nguyenkduy28/vlc-system-project/ref/Block diagram/Bit Sampling Process for-2026-04-19-093058.png

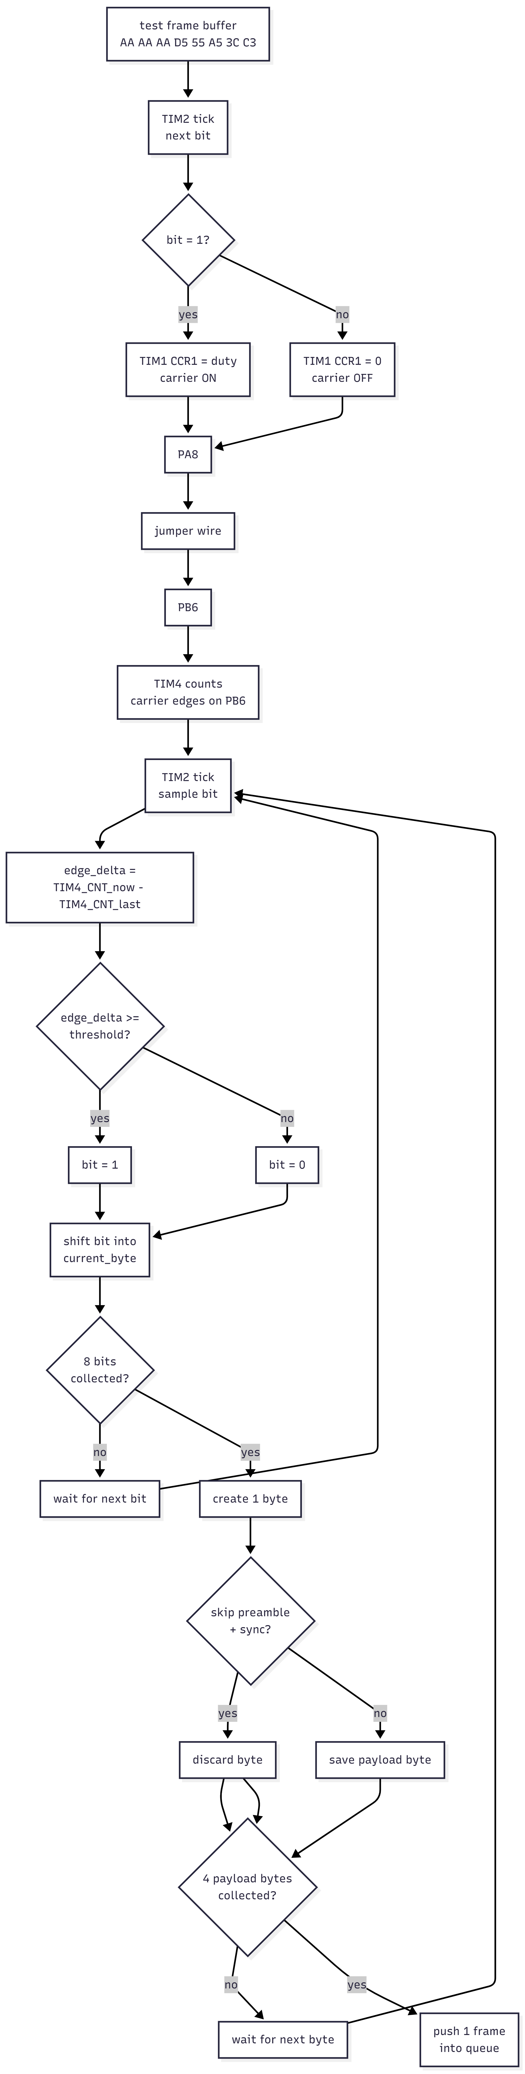
ref/Block diagram/Bit Sampling Process for-2026-04-19-093058.png
