nguyenkduy28/vlc-system-project/ref/Block diagram/TX_IDLE to CARRIER ON Flow-2026-04-19-093544.png

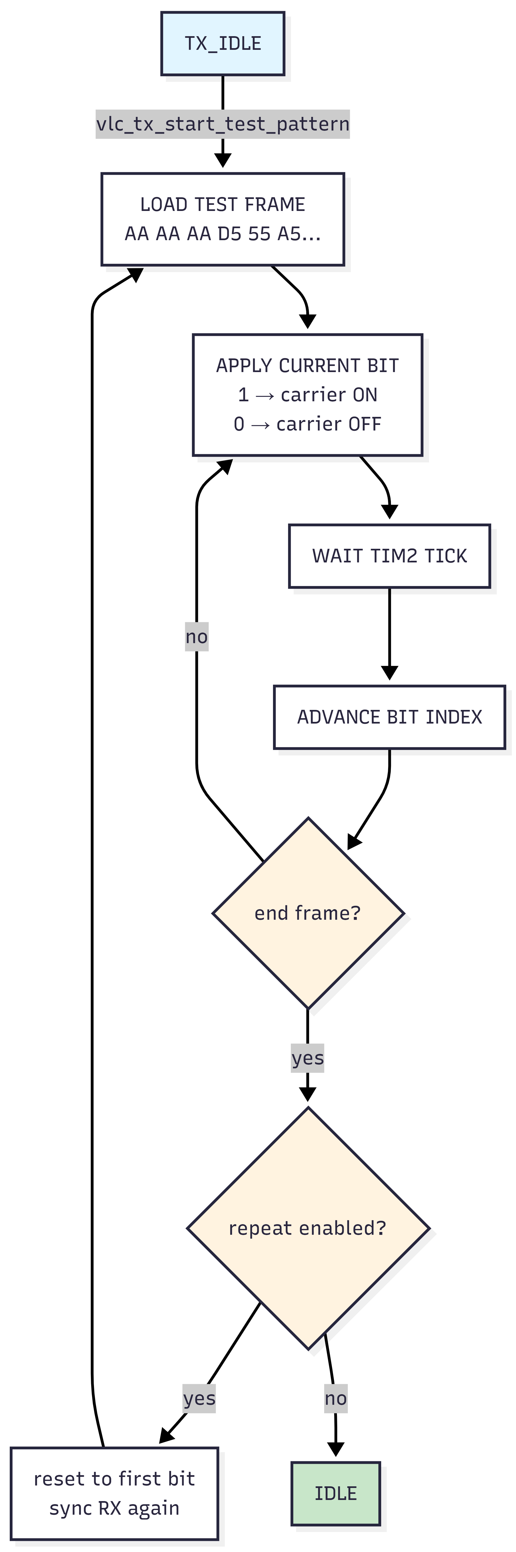
ref/Block diagram/TX_IDLE to CARRIER ON Flow-2026-04-19-093544.png
