nguyenkduy28/vlc-system-project/ref/FILTER/HPF_1KHZ.jpg

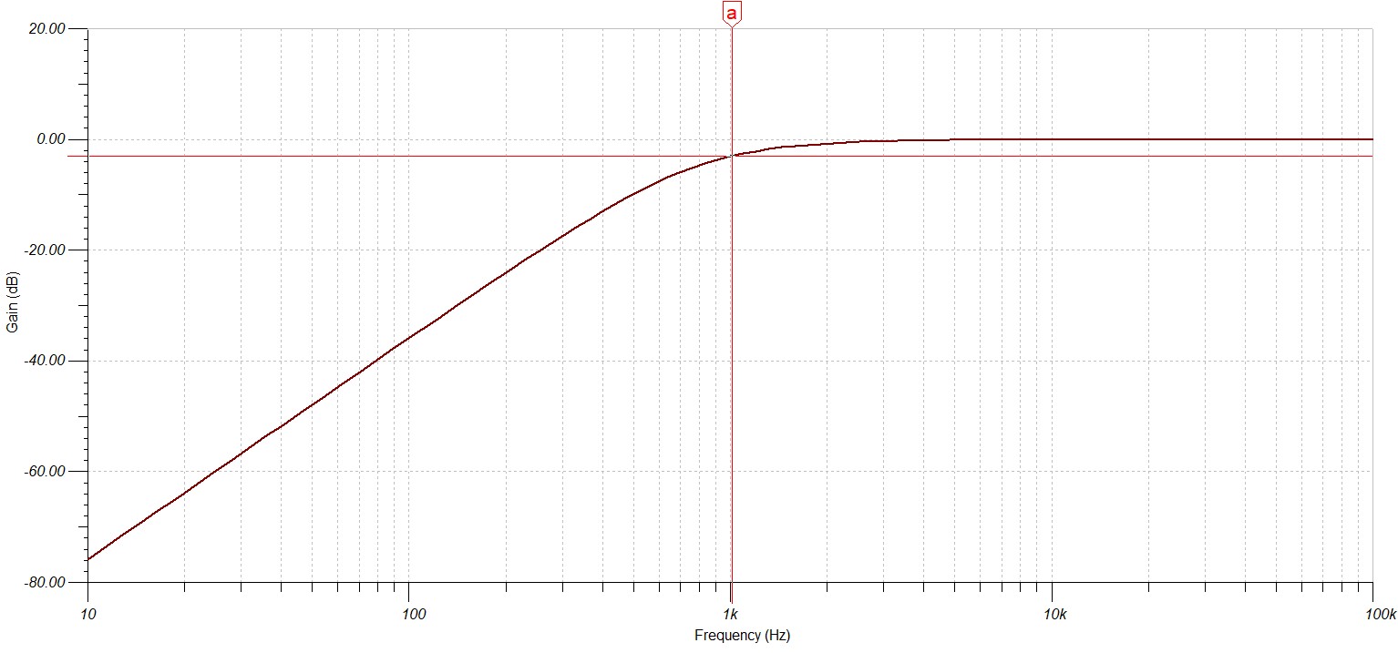
ref/FILTER/HPF_1KHZ.jpg
