nguyenkduy28/vlc-system-project/ref/ING/BU_8MHz.png

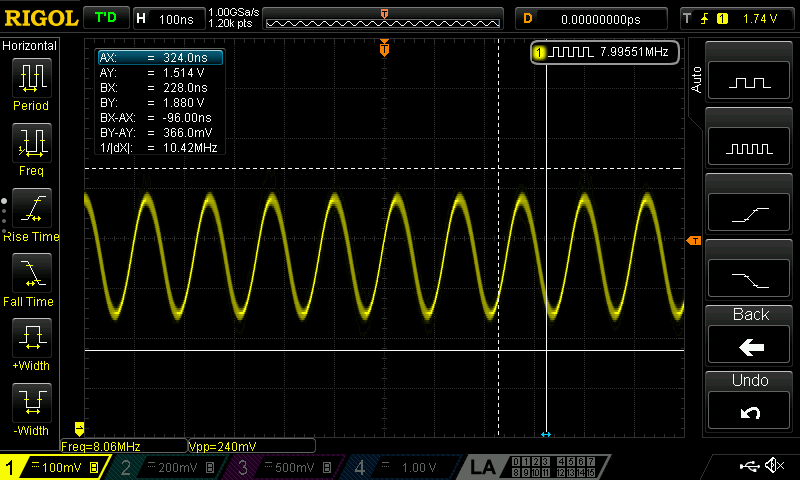
ref/ING/BU_8MHz.png
