nguyenkduy28/vlc-system-project/ref/ING/Carrier_1Mhz.png

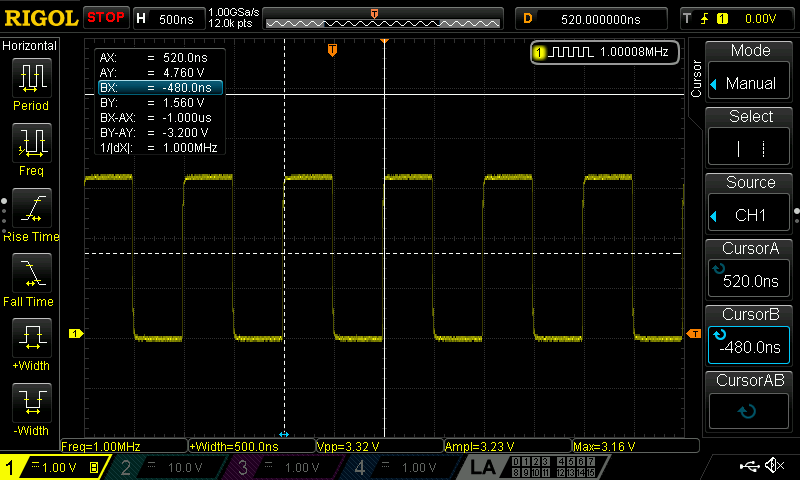
ref/ING/Carrier_1Mhz.png
