nguyenkduy28/vlc-system-project/ref/ING/flow.png

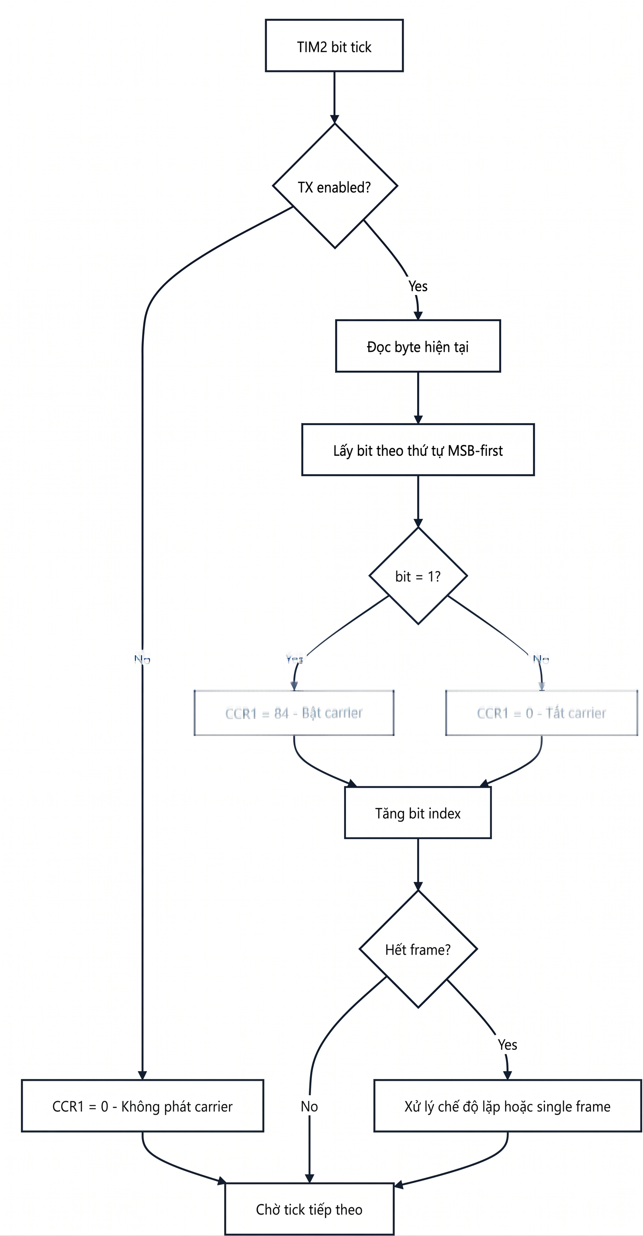
ref/ING/flow.png
