nguyenkduy28/vlc-system-project/ref/ING/layer.png

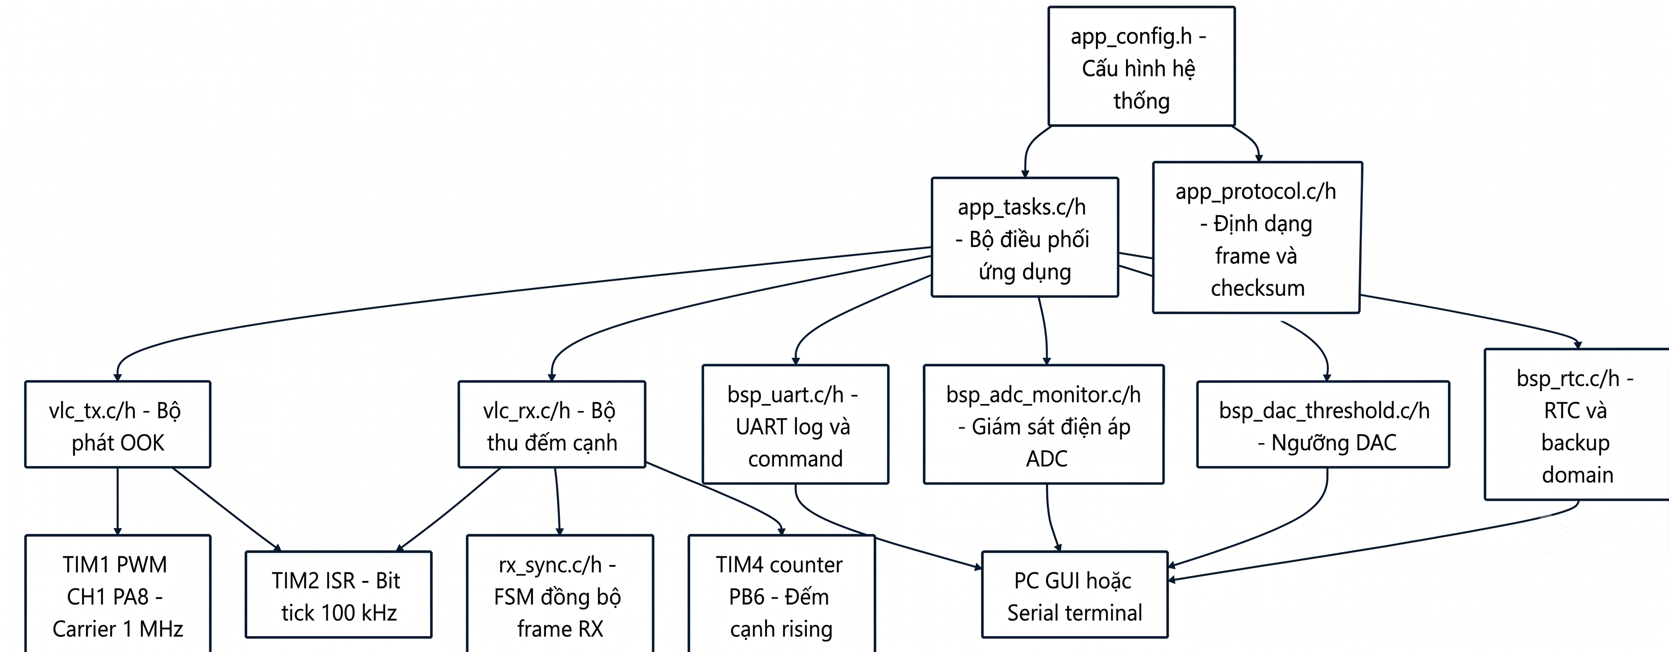
ref/ING/layer.png
