nguyenkduy28/vlc-system-project/ref/ING/MCO_BU_CLOCK.png

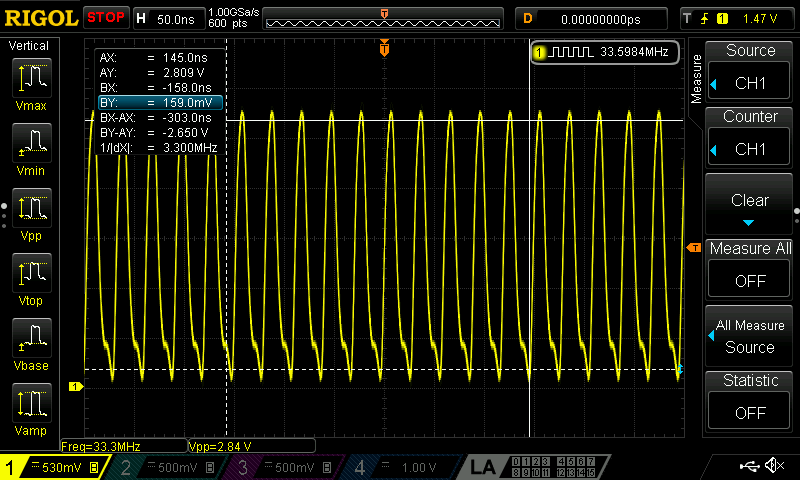
ref/ING/MCO_BU_CLOCK.png
