nguyenkduy28/vlc-system-project/ref/ING/Modulation_100kHz_OOK.png

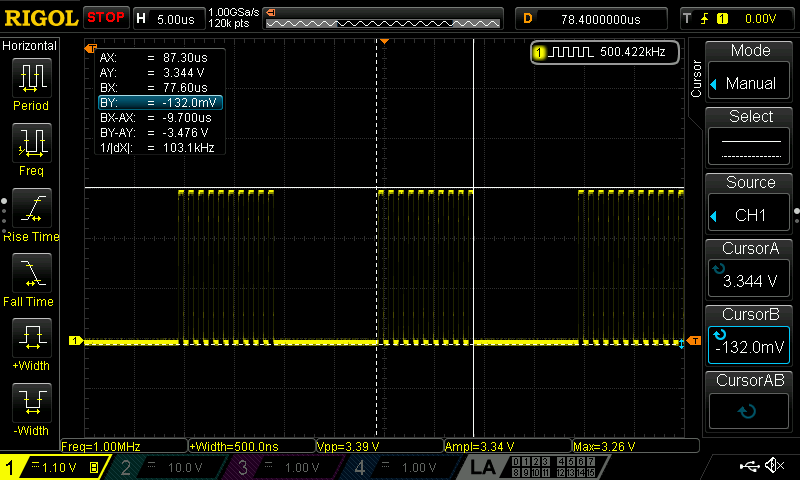
ref/ING/Modulation_100kHz_OOK.png
