nguyenkduy28/vlc-system-project/ref/ING/PD_Seq.png

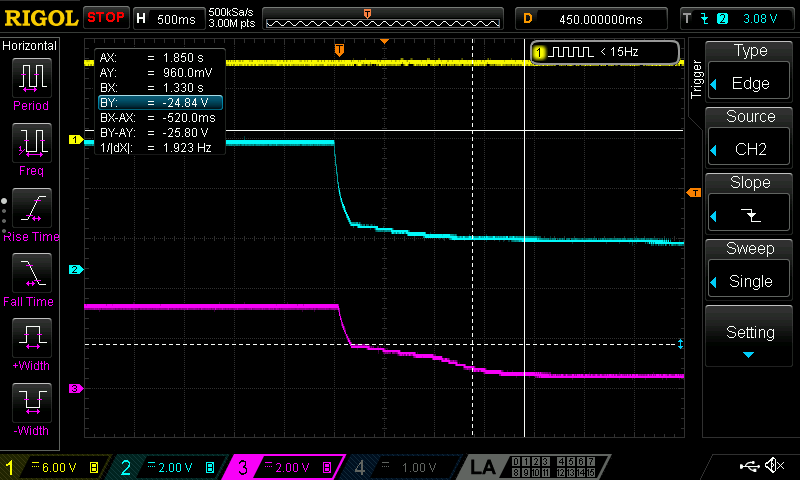
ref/ING/PD_Seq.png
