nguyenkduy28/vlc-system-project/ref/ING/PU_Seq.png

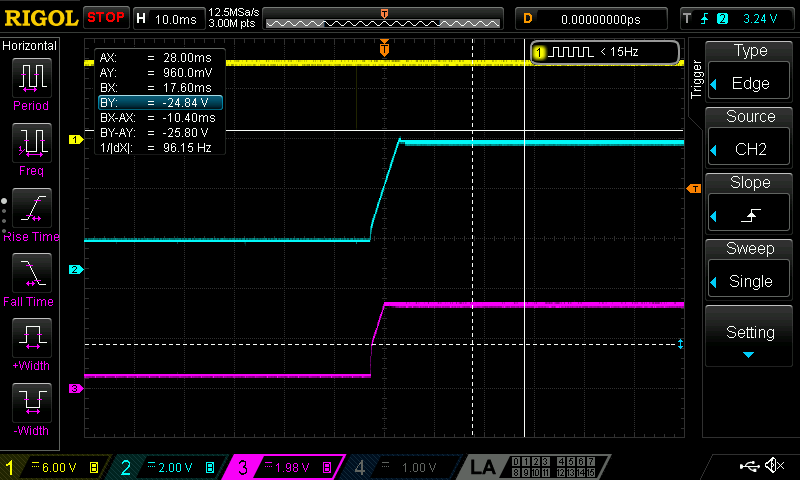
ref/ING/PU_Seq.png
