nguyenkduy28/vlc-system-project/ref/ING/right.png

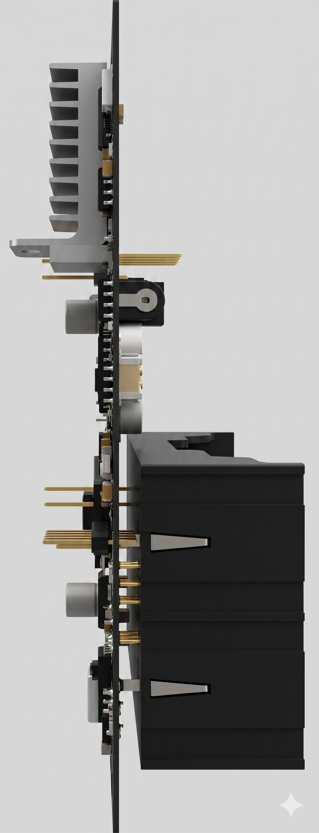
ref/ING/right.png
