nguyenkduy28/vlc-system-project/ref/ING/TC4427_DLTN23.png

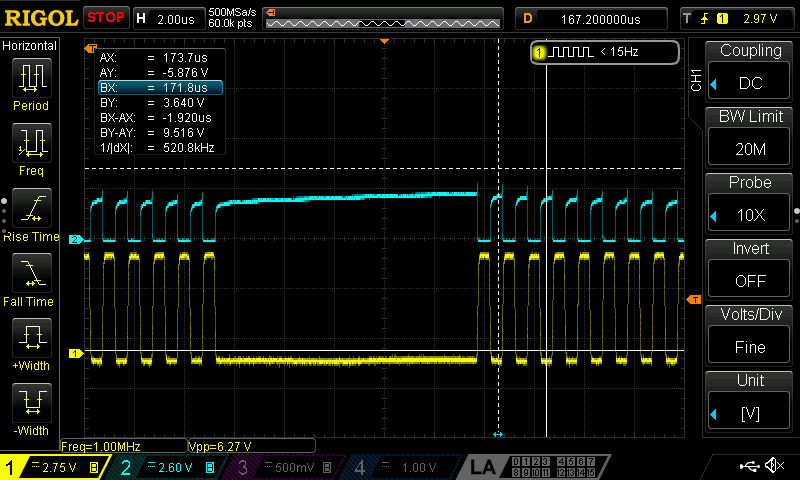
ref/ING/TC4427_DLTN23.png
