nguyenkduy28/vlc-system-project/ref/ING/tx.png

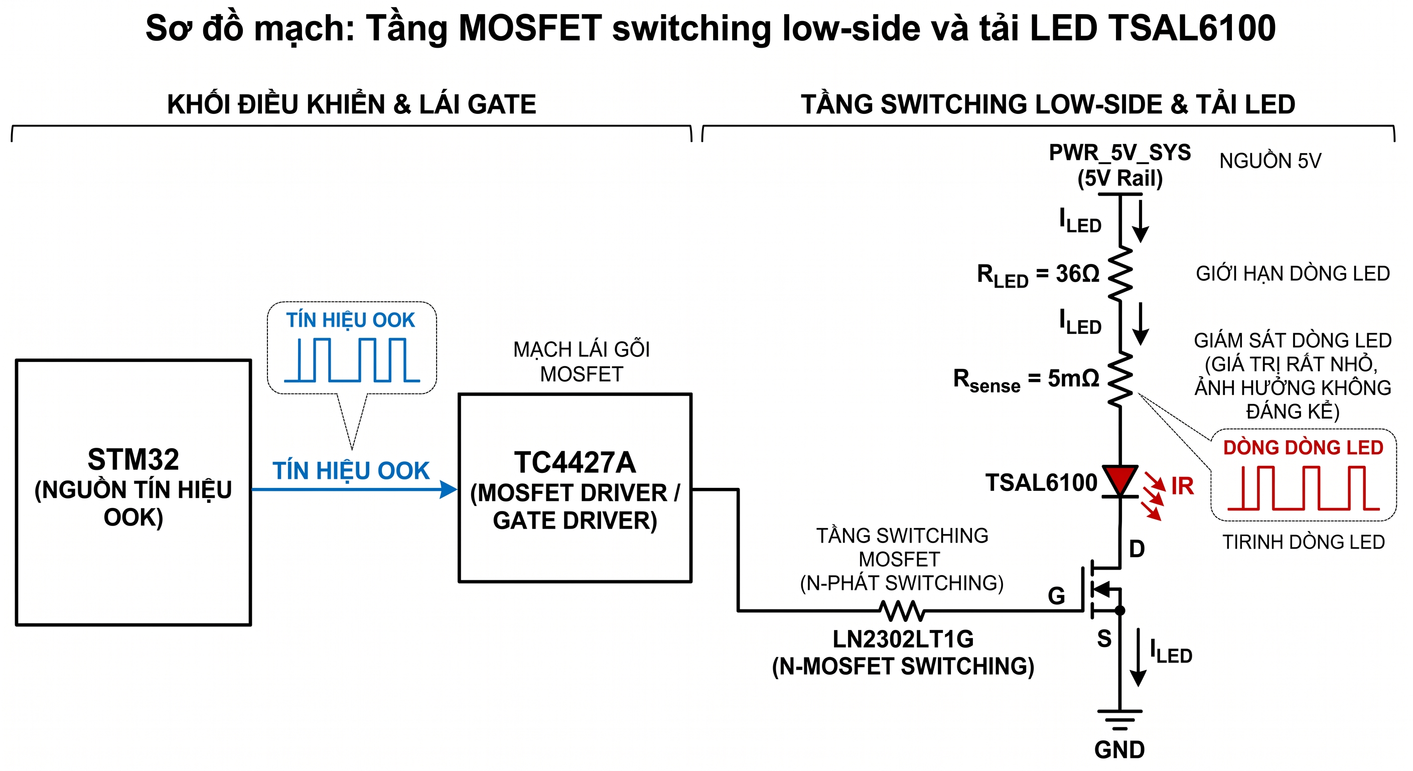
ref/ING/tx.png
