nguyenkduy28/vlc-system-project/ref/ING/Voltage_Ripple.png

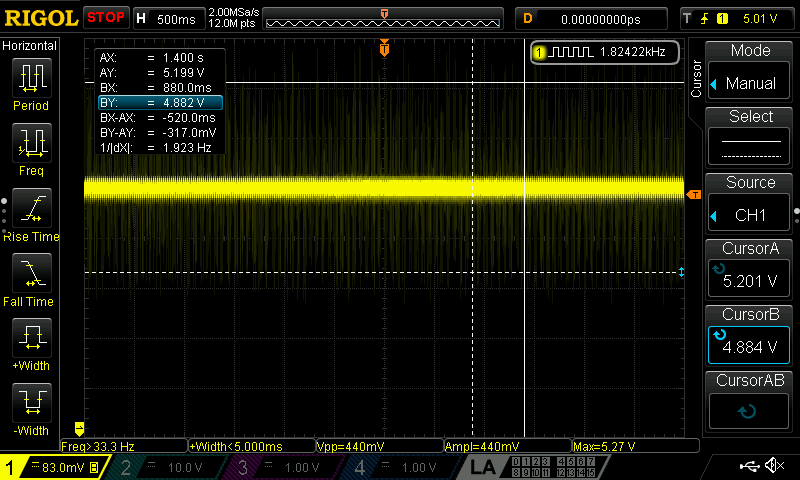
ref/ING/Voltage_Ripple.png
