nguyenkduy28/vlc-system-project/ref/ING/DS1Z_QuickPrint2.png

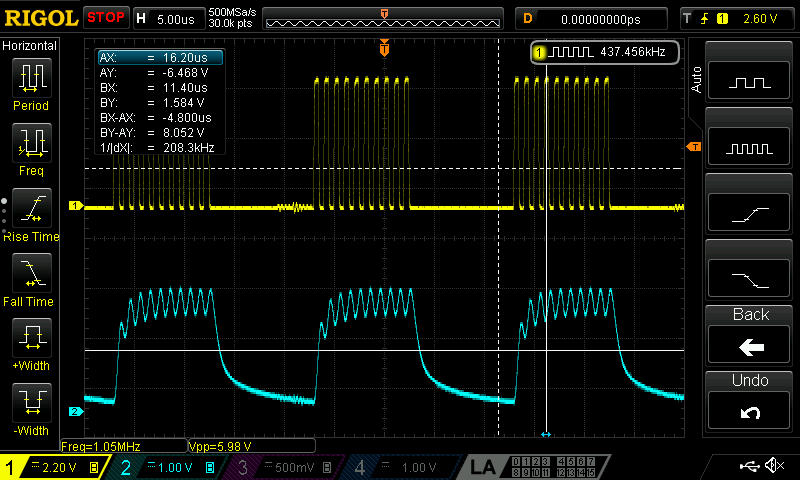
ref/ING/DS1Z_QuickPrint2.png
