nguyenkduy28/vlc-system-project/ref/ING/DS1Z_QuickPrint6.png

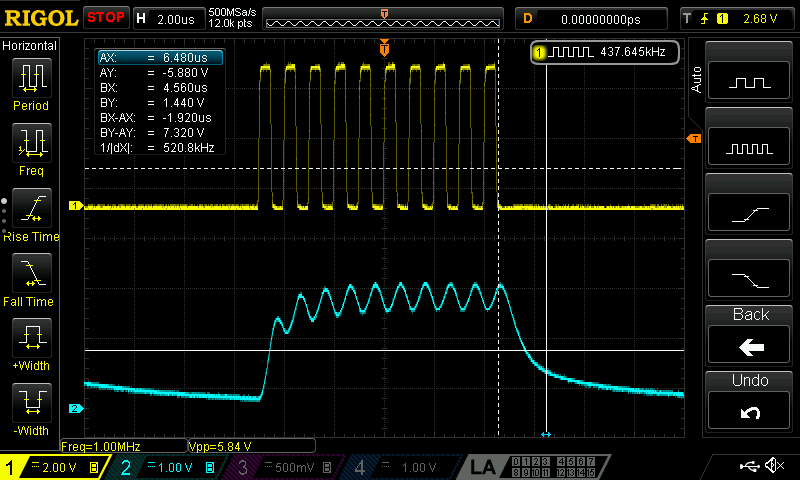
ref/ING/DS1Z_QuickPrint6.png
