nguyenkduy28/vlc-system-project/ref/ING/DS1Z_QuickPrint16.png

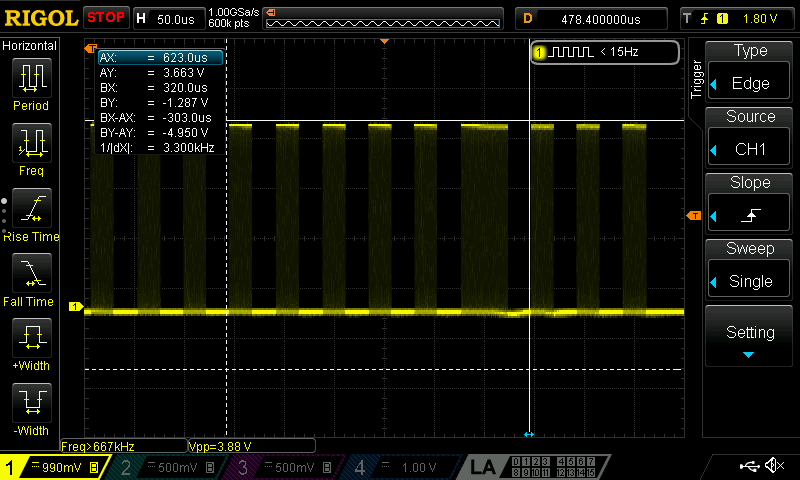
ref/ING/DS1Z_QuickPrint16.png
