nguyenkduy28/vlc-system-project/ref/ING/Bug_clock.png

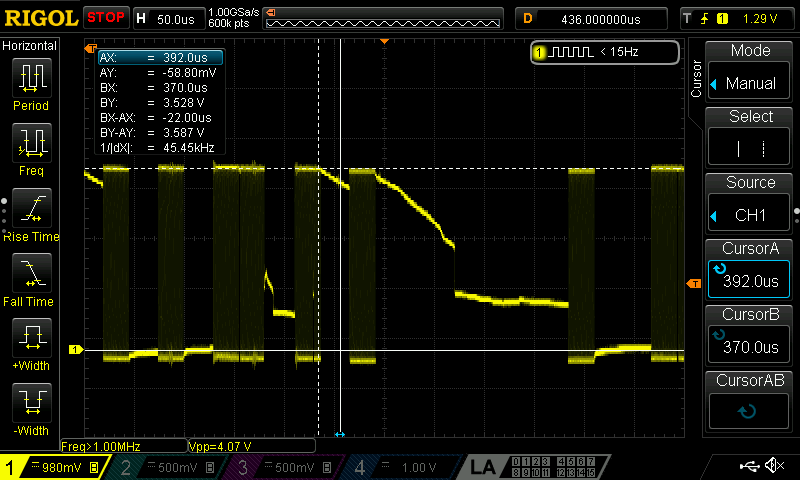
ref/ING/Bug_clock.png
