nguyenkduy28/vlc-system-project/ref/ING/bug_tc4427.png

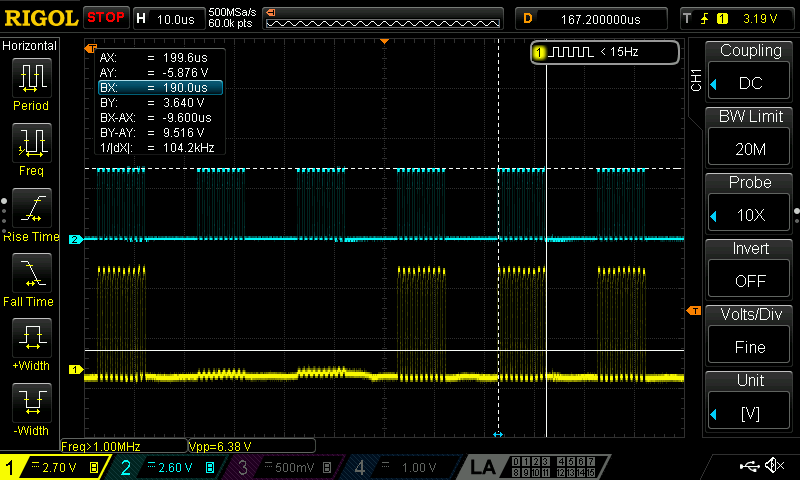
ref/ING/bug_tc4427.png
