nguyenkduy28/vlc-system-project/firmware/Core/Inc/board_pins.h

#ifndef BOARD_PINS_H
#define BOARD_PINS_H

#include "main.h"

#define PIN_RX_OUT_D_GPIO_Port      GPIOB
#define PIN_RX_OUT_D_Pin            GPIO_PIN_6

#define PIN_TX_READY_GPIO_Port      GPIOD
#define PIN_TX_READY_Pin            GPIO_PIN_13

#define PIN_RX_READY_GPIO_Port      GPIOD
#define PIN_RX_READY_Pin            GPIO_PIN_15

#endif
